pymo/ppk_bluetooth/3d_print/version2/upper_cap.stl

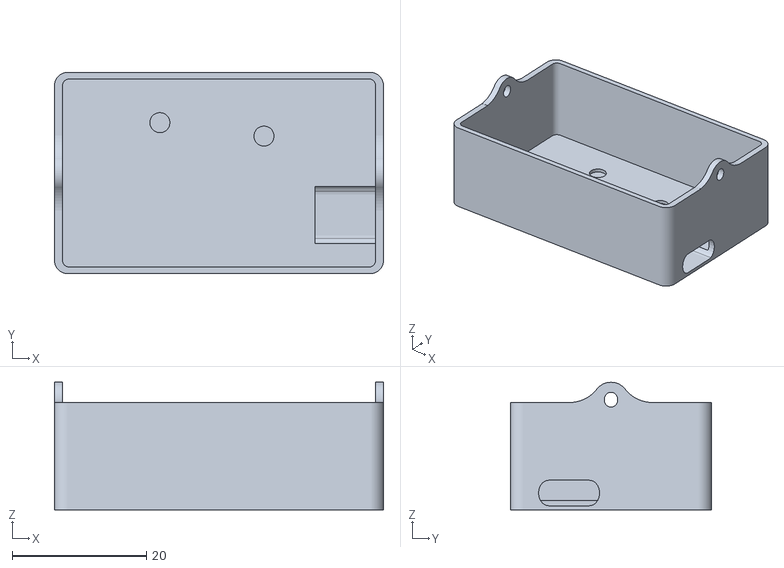
[picture p17: CAD file, 2022-05-05, an earlier design]
3d_print/version2/upper_cap.stl
49.0 x 30.0 x 19.0
