pymo/ppk_bluetooth/3d_print/version2/board_clips.stl

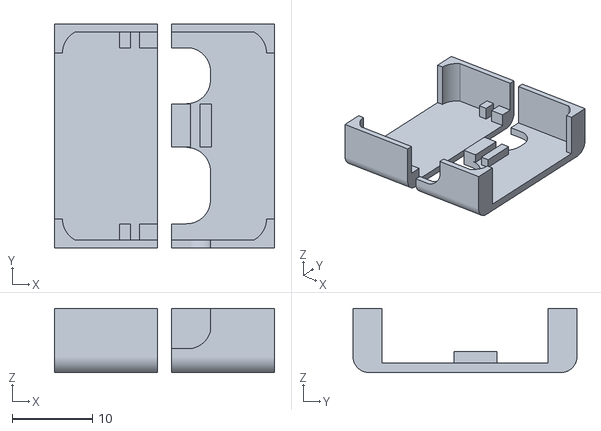
[picture p18: CAD file, 2022-05-05, an earlier design]
3d_print/version2/board_clips.stl
27.5 x 28.0 x 8.00
