pymo/ppk_bluetooth/3d_print/version2/battery_spacer.stl

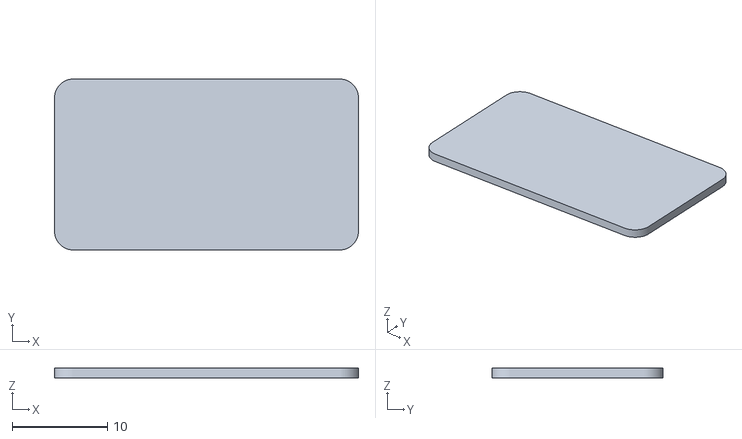
[picture p19: CAD file, 2022-04-26, an earlier design]
3d_print/version2/battery_spacer.stl
32.0 x 18.0 x 1.00
